TXWD1234/TXCompute/docs/zine-page/final-render.png

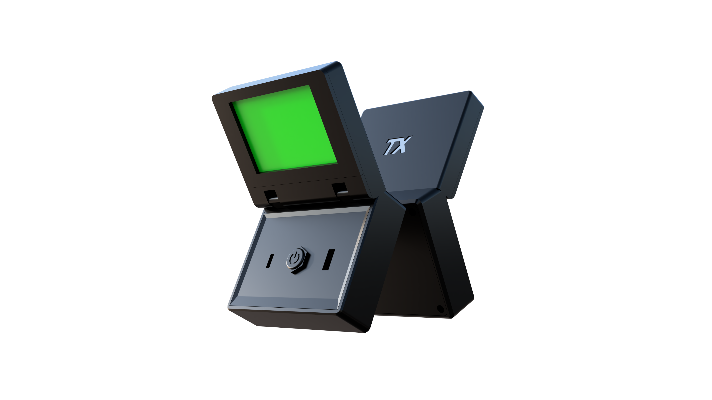
docs/zine-page/final-render.png
